cheyao/fireflies/pcb/spice-simulation.asc

R1: res; 2200
U1: UniversalOpAmp2; Avol=177827.941 GBW=12Meg Slew=7.7Meg; Ilimit=1.5m Rail=35m Vos=0
U2: 4N25
V1: voltage; PULSE(0 3.3 200u 10u 10u 10u 500u 50000)
V2: voltage; 3.3
Named nets: 0, 3v3, diode
.tran 0 11m 10m uic
